agios/zerog-enclosure/STL/top/mini_hinge_back.stl

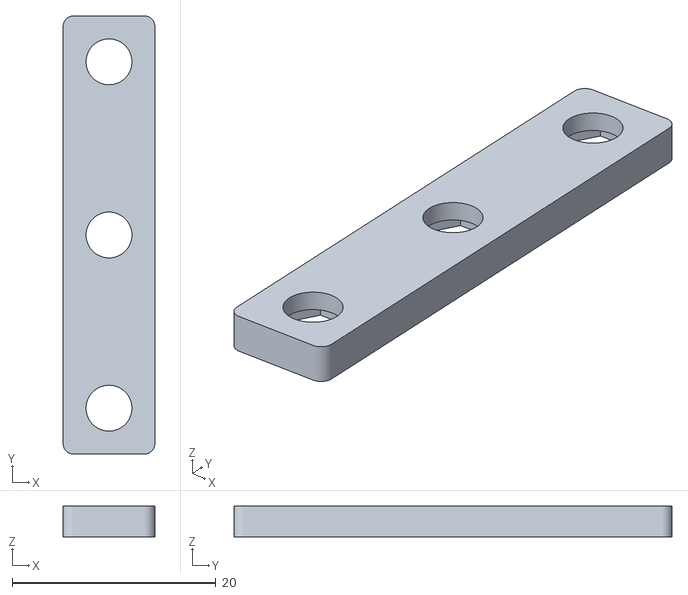
[picture p22: CAD file, 2024-11-05]
STL/top/mini_hinge_back.stl
9.00 x 43.0 x 3.00
