agios/zerog-enclosure/DXF/door.dxf

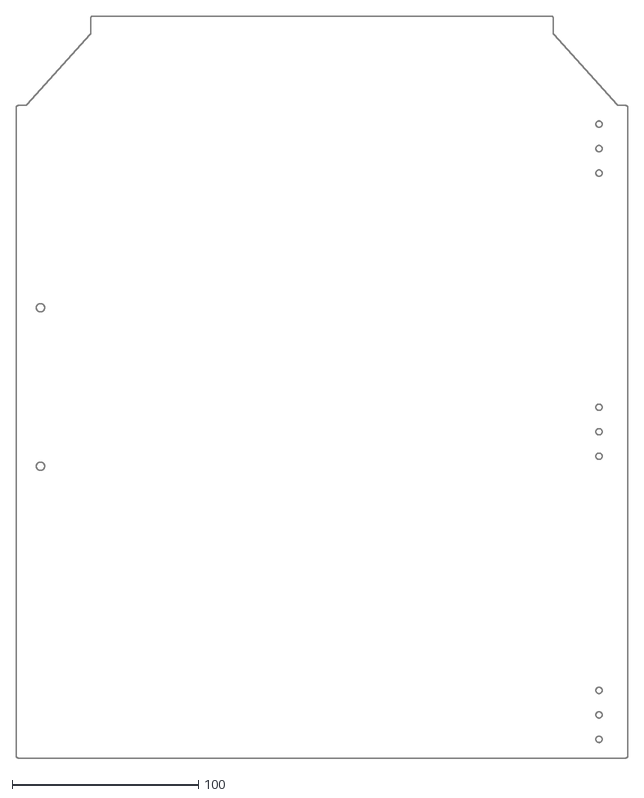
[picture p23: CAD file, 2024-11-05]
DXF/door.dxf
328.0 x 398.0
