agios/zerog-enclosure/STL/top/front_right_corner_cover_w_notch.stl

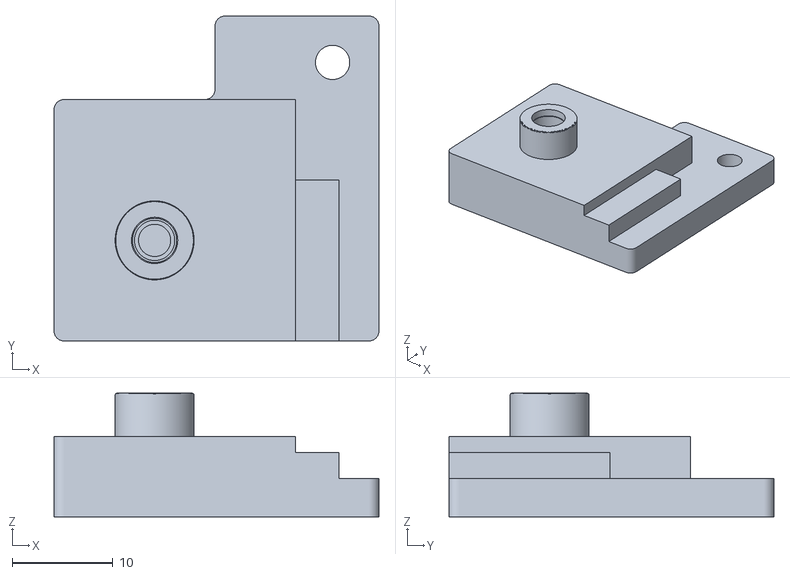
[picture p24: CAD file, 2024-11-05]
STL/top/front_right_corner_cover_w_notch.stl
32.3 x 32.3 x 12.3
