agios/zerog-enclosure/STL/mount/rear_top_center.stl

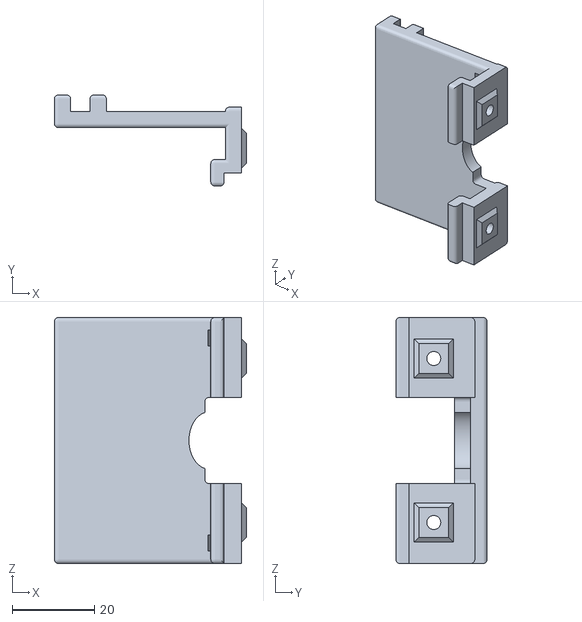
[picture p25: CAD file, 2024-11-05]
STL/mount/rear_top_center.stl
46.9 x 22.2 x 60.0
