agios/zerog-enclosure/STL/top/corner_cover_flange.stl

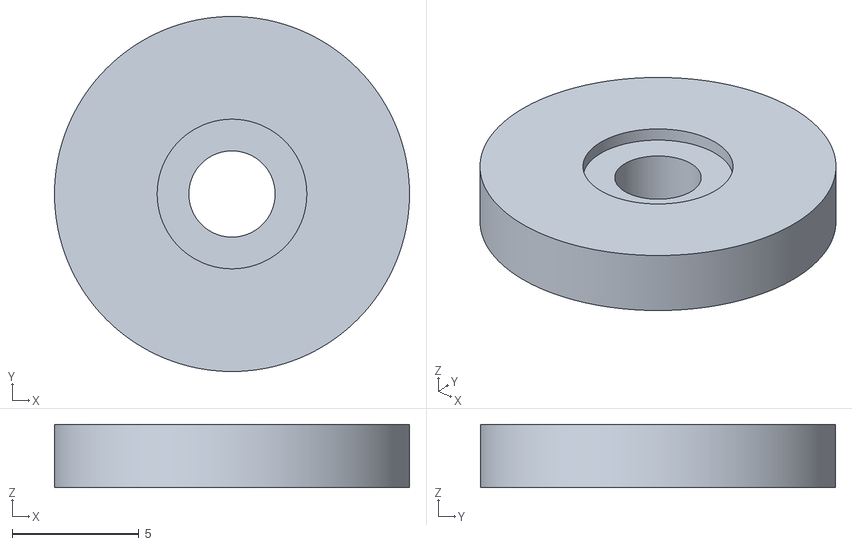
[picture p26: CAD file, 2024-11-05]
STL/top/corner_cover_flange.stl
14.0 x 14.0 x 2.50
