agios/zerog-enclosure/STL/mount/front_184.stl

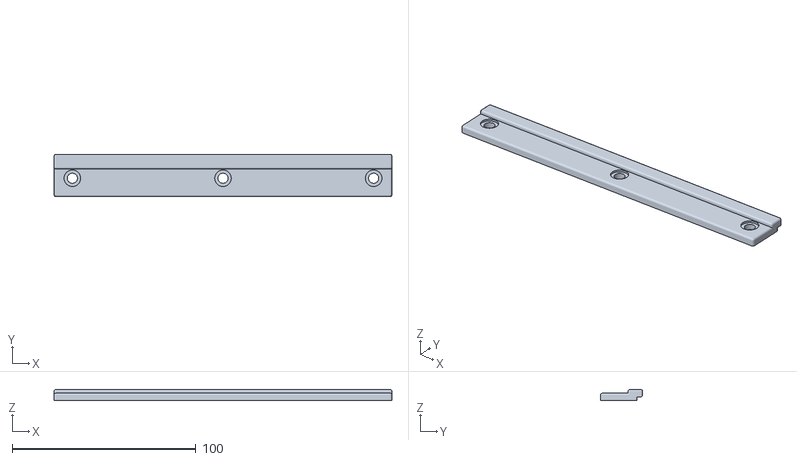
[picture p27: CAD file, 2024-11-05]
STL/mount/front_184.stl
184.0 x 23.0 x 6.01
