agios/zerog-enclosure/STL/mount/side_130.stl

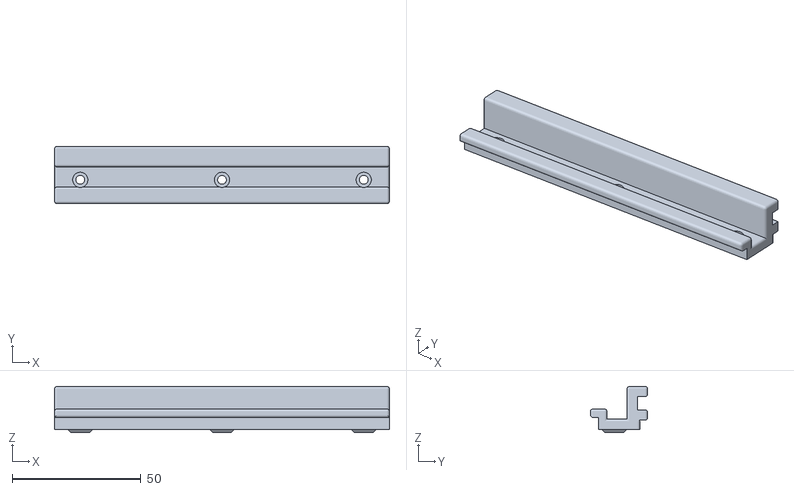
[picture p28: CAD file, 2024-11-05]
STL/mount/side_130.stl
130.0 x 22.2 x 17.9
