agios/zerog-enclosure/SCAD/bottom/door_projection.scad

include <door.scad>

projection(cut = false) door();
