agios/zerog-enclosure/SCAD/bottom/door_stop.scad

include <../door_magnet.scad>

rotate([0, 0, 90])
door_stop(clearance=4, offset=6.8, screw_support=false);
