agios/zerog-enclosure/SCAD/mount/front_184.scad

include <../config.scad>
include <mount.scad>

mount(184, top = str("face,d=", panel_front_distance), add_screw_supports = false);
