agios/zerog-enclosure/SCAD/mount/rear_center_150.scad

include <../config.scad>
include <mount.scad>

mount(150,
      top = "latch",
      bottom = "latch",
      counterbore = 3,
      add_zip_mounts = true);
