agios/zerog-enclosure/SCAD/mount/rear_center_80.scad

include <../config.scad>
include <mount.scad>

mount(80,
      top = "latch",
      bottom = "latch",
      counterbore = 3,
      add_zip_mounts = true);
