agios/zerog-enclosure/SCAD/mount/side_130.scad

include <mount.scad>

mount(130, top = "slot,d=8", bottom = "latch");
