agios/zerog-enclosure/SCAD/mount/side_50.scad

include <mount.scad>

mount(50, top = "slot,d=8", bottom = "latch");
