agios/zerog-enclosure/SCAD/mount/side_front_left.scad

include <mount.scad>

mount(60,
      top = "slot,d=8",
      bottom = "latch,r+8");
