agios/zerog-enclosure/SCAD/mount/side_front_right.scad

include <mount.scad>

mount(60,
      top = "slot,d=8",
      bottom = "latch,l+8");
