agios/zerog-enclosure/SCAD/mount/side_rear_left.scad

include <mount.scad>

extend_rear = panel_rear_distance - corner_size - mount_thickness;
mount(70,
      top = str("slot,d=8,l+", extend_rear),
      bottom = "latch,l-15");
