agios/zerog-enclosure/SCAD/top/corner_cover_w_notch.scad

include <corner.scad>

rotate([180, 0, 0])
corner_cover_w_notch();
