agios/zerog-enclosure/SCAD/top/corner_front_left.scad

include <corner.scad>

front_corner();
