agios/zerog-enclosure/SCAD/top/corner_front_right.scad

include <corner.scad>

mirror([1, 0, 0]) front_corner();
