agios/zerog-enclosure/SCAD/top/corner_rear.scad

include <corner.scad>

corner();
