agios/zerog-enclosure/SCAD/top/cover_front_projection.scad

include <cover_front.scad>

projection(cut = false) cover_front();
