agios/zerog-enclosure/SCAD/top/cover_rear_projection.scad

include <cover_rear.scad>

projection(cut = false) cover_rear();
