agios/zerog-enclosure/SCAD/top/cover_side_projection.scad

include <cover_side.scad>

projection(cut = false) cover_side();
