agios/zerog-enclosure/SCAD/top/cover_top_projection.scad

include <cover_top.scad>

projection(cut = false) cover_top();
