agios/zerog-enclosure/SCAD/top/door_handle_back.scad

include <../door_magnet.scad>

rotate([0, 0, 90])
door_handle_back(thickness=6);
