agios/zerog-enclosure/SCAD/top/door_stop.scad

include <../door_magnet.scad>

rotate([0, 0, 90])
door_stop(stop_position=0, offset=5.3, screw_support=false);
