agios/zerog-enclosure/SCAD/top/front_left_corner_cover_w_notch.scad

include <corner.scad>

rotate([180, 0, 0])
front_corner_cover_w_notch();
