agios/zerog-enclosure/SCAD/top/front_right_corner_cover_w_notch.scad

include <corner.scad>

rotate([180, 0, 0]) mirror([1, 0, 0])
front_corner_cover_w_notch();
